jevans3142/adc-boxes-video-controls/src/main/main.h

// LX/Sound boxes video control panels

#ifndef MAIN_H_INCLUDED
#define MAIN_H_INCLUDED

// Used for commands in queue to input logic
struct Queued_Input_Message_Struct {
    uint8_t type; // See below defines

    uint8_t panel_button; // Used for a routing command (which button within the panel)

    uint8_t input; // Used for an incoming routing confirm
    uint8_t output; // Used for an incoming routing confirm 
};

// Definitions of message type for input messages 
#define IN_MSG_TYP_ROUTING 0
#define IN_MSG_TYP_ETHERNET 1

#endif
